ALSETLab/FluxPMU/00_Documentation/03_LabVIEW_VI_Documentation/24 Global Front Panel.pdf

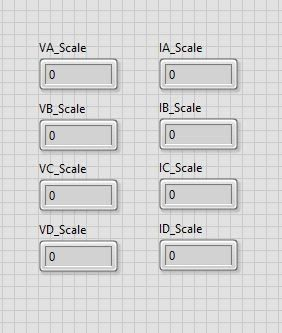
[picture p25: figure]

24 Global Front Panel is just used to output the global scale variables for voltages and currents a-d. The global variables are set in 43 Config File Get Input Scales. Note that 24 Global Front Panel does not have a block diagram, as the only output is from global variables.
