ALSETLab/FluxPMU/00_Documentation/03_LabVIEW_VI_Documentation/33 GPS Time to Labview Time.pdf

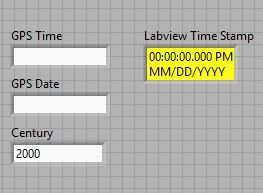
[picture p26: figure]

33 GPS Time to LabVIEW Time takes three inputs, the GPS Time, GPS Date, and the Century to output the time in a similar format in LabVIEW, used for creating a global time variable to create the synchrophasors. The Front Panel (above) displays all of this information.

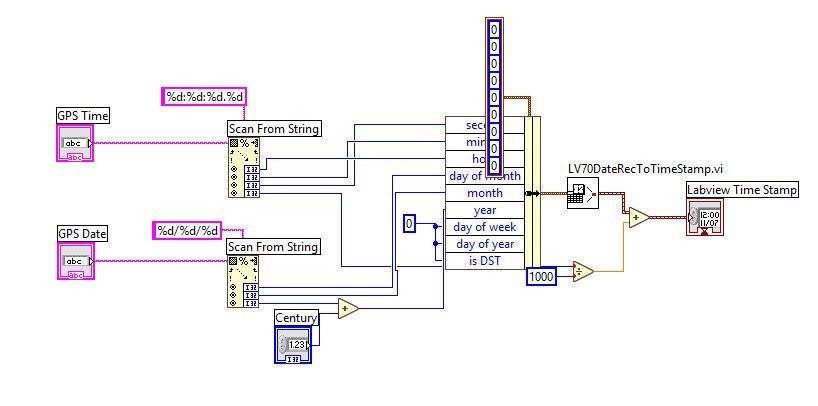
[picture p27: figure]

The Block Diagram (above) starts with the input GPS Time and GPS Date. ATTENTION: The GPS Time must be input in the format HR:MIN:SS.MSS The Date must be input in the format DD/MM/YY NOT MM/DD/YYYY. Both the GPS Time and GPS Date are converted into strings based on the format as stated in ATTENTION. Each string value excluding the millisecond time is bundled to a cluster, and converted into a LabVIEW Time Stamp. LabVIEW Time Stamp does not support millisecond when bundling, so the millisecond value is added to the Time Stamp once it has been created. The Time Stamp is then sent to the Front Panel as output. The output time has the same format as above, but the output date is sent in the format of MM/DD/YYYY
