ALSETLab/FluxPMU/00_Documentation/03_LabVIEW_VI_Documentation/34 GPS Time from Config.pdf

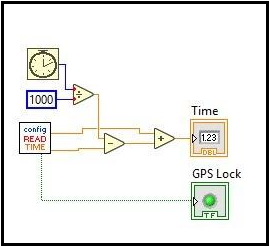
[picture p28: figure]

34 GPS Time from Config VI outputs the Time by first finding the difference between the Tick Count and the millisecond counter in microseconds. These values come from the VI 42 Config File Read GPS Time. The difference is added to the LabVIEW time to output the Time. The VI also outputs if the GPS lock is True or False based on 42 Config File Read GPS Time.
