ALSETLab/FluxPMU/00_Documentation/03_LabVIEW_VI_Documentation/15 Triple Phase Signal Generation.pdf

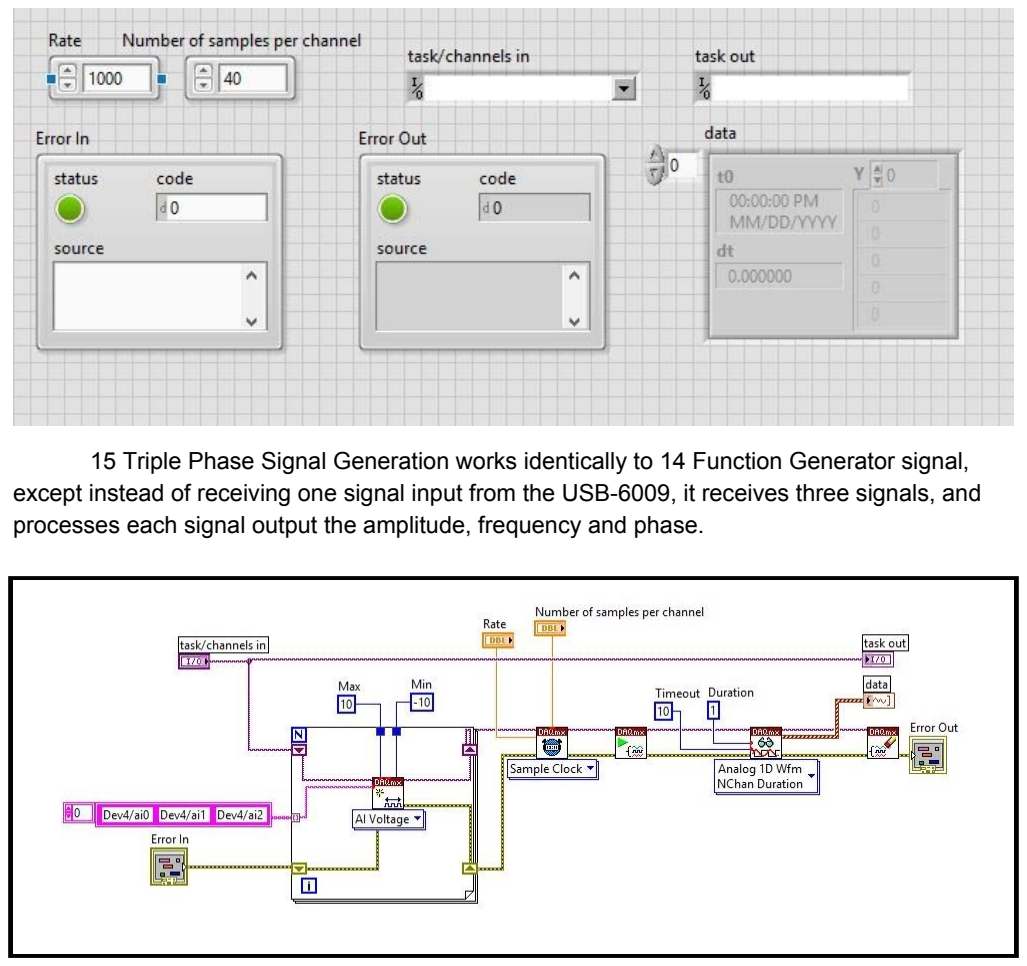
[picture p35: page 1]

15 Triple Phase Signal Generation works identically to 14 Function Generator signal, except instead of receiving one signal input from the USB-6009, it receives three signals, and processes each signal output the amplitude, frequency and phase.
