ALSETLab/FluxPMU/00_Documentation/03_LabVIEW_VI_Documentation/30 GPS Time Fetch.pdf

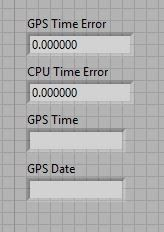
[picture p38: figure]

30 GPS Time Fetch is used to find the time in order to create a time synchronous system. The image above shows the Front Panel. The GPS Time, Date, and Time Error are outputted, along with the CPU Time Error.

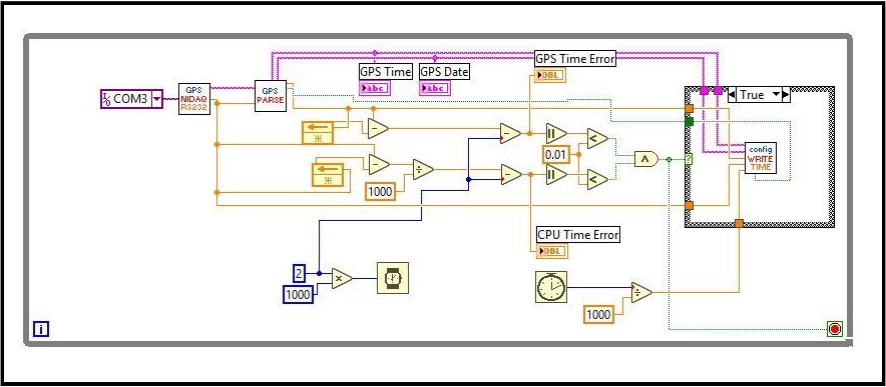
[picture p39: figure]

ATTENTION: The I/O COM# may have to be changed for your Garmin GPS set up.

Above shows the Block Diagram. 30 GPS Time Fetch continuously finds the time from the Garmin GPS signal by using a While Loop, and several sub-VIs to determine a synchronous time. GPS Time Fetch begins by receiving an input the Garmin GPS at a COM input port. You will need to set the port number here, based on what port you plug the RS-232 Cable into. Use Windows Device Manager to easily find what port number you need.
Two signals are sent:
- The Pink Line, the GPS data is sent to 31GPS NIDAQ RS232 sub-VI for Data processing. The output data of the sub-VI is sent to another sub-VI, 32 GPS PARSE, for further processing. 32 GPS PARSE outputs the Time, Date, which are sent to the Front Panel, and to the Case Structure.
- The Orange Line, the CPU data, is sent through various logic structures to calculate both the GPS Time Error and the CPU Time Error, which are sent to the Front Panel. If both the errors satisfy the condition of being less than 0.01 two things happen. The Case Structure is satisfied, and writes all of the data found to 41 Config File Write GPS Time, and the while loop stops.
Once computed, the GPS Time Error, CPU Time Error, GPS Time and GPS Date are all written via 41 Config File Write GPS Time, to be used by 34 GPS Time From Config in processing the time.
