ALSETLab/FluxPMU/00_Documentation/03_LabVIEW_VI_Documentation/31 GPS Interrupt RS232 Read.pdf

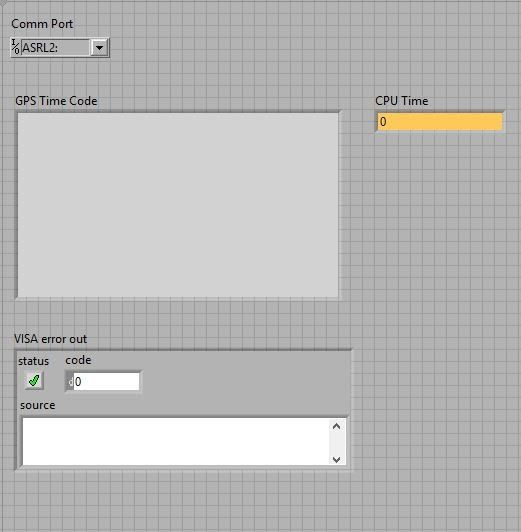
[picture p40: figure]

31 GPS Interrupt RS232 Read takes a COM port and uses the VISA program to produce the GPS Time Code. The Time code is sent to various other VIs to be used as the time Synchronous component in analysis.

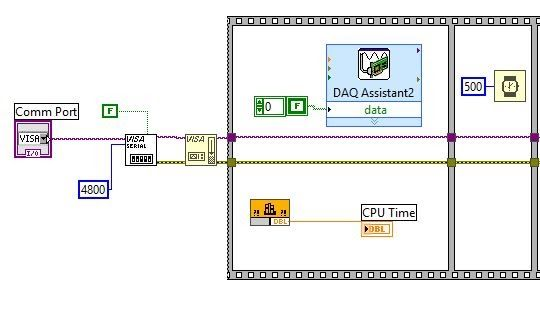
[picture p41: figure]

The VI starts by receiving the port resource name, or the COMM port specified in 30 GPS Time Fetch. The port information is sent to the VISA Configure Serial Port, which also is inputted with the baud rate. The VISA resource name and any errors are sent through a VISA buffer. After the buffer, the Flat sequence portion of code is activated. The first box uses the NI_Timer.dll to find the CPU time, which is used to compare to the GPS time. The DAQ Assistant 2 sets a task. The second box in the flat sequence waits for half a second.

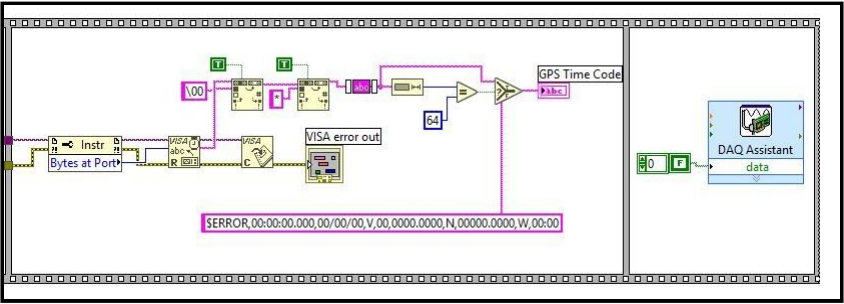
[picture p42: figure]

The third box in the flat sequence begins by receiving the VISA resource name, and returns the byte at that port. Both of these are sent to a buffer, which returns the resource name again, and the data at the port in a read buffer as a string. In the bottom portion, the VISA is closed, and any errors are sent to the Front Panel. In the above portion, the string is sent to a search and replace in the string twice. Once complete, the whitespace is trimmed, and the length is calculated. Based on the length, either the correct GPS Time code is produced, or an Error code is returned. Once complete, the final part of the flat sequence closes the task.

When you run the VI you have to make sure to NOT have HyperTerminal/Access running at the same time. If a Hyper program is running, you will get a VISA error, stating that the GPS signal cannot be accessed. Even if everything else is set up/running correctly, if either of the Hyper programs are connected, this VI will not work.
When you run the VI with either Hyper program connected, the GPS time code will be outputted in the Hyper Program, as shown below.

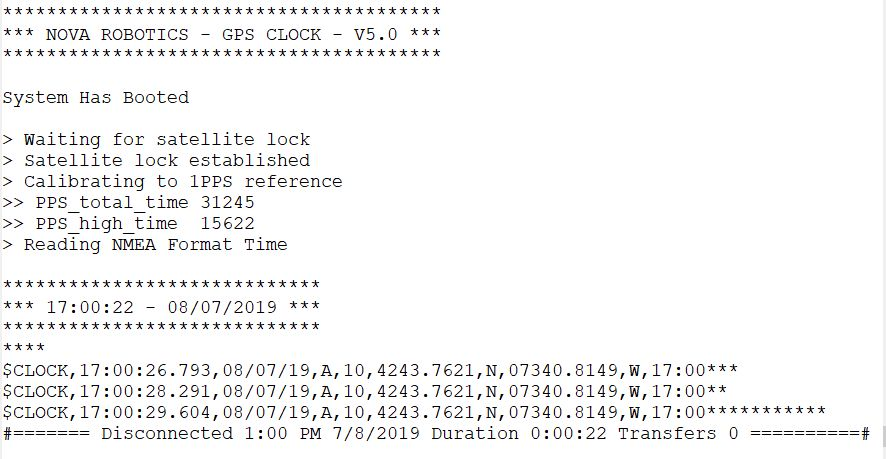
[picture p43: figure]

The image above shows the output when connecting simultaneously being connected to HyperAccess and LabVIEW. Each GPS time code line represents running the VI once.
