ALSETLab/FluxPMU/00_Documentation/03_LabVIEW_VI_Documentation/38 Date Conversion.pdf

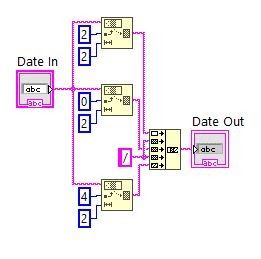
[picture p52: figure]
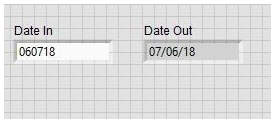
[picture p53: figure]

38 Date Conversion works in a similar manner to 37 Time Conversion. The Date string is inputted and split, as the input date is represented by DDMMYY. The split strings are concatenated, along with adding ‘/’ in between each two characters, to output the correct Date data in the format MM/DD/YY.
