ALSETLab/FluxPMU/00_Documentation/03_LabVIEW_VI_Documentation/40 Config File Path.pdf

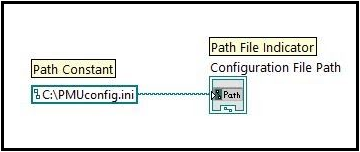
[picture p57: figure]

ATTENTION: The Path Constant will have to change based on YOUR file locations.

40 Config File Path is used to set the right path for OpenPMU files to communicate. The image on the left shows the Path Constant on the Front Panel. The image on the right shows the Path Constant set in the Block Diagram. ATTENTION: The Path Constant will have to change based on YOUR file locations. The Path Constant is given to the file path indicator, which sets the file path for the OpenPMU programs to use.
