ALSETLab/FluxPMU/00_Documentation/03_LabVIEW_VI_Documentation/42 Config File Read GPS Time.pdf

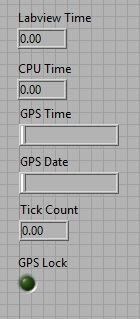
[picture p60: figure]

42 Config File Read GPS Time VI outputs various variables written to GPS_time.ini in the VI 41 Config File Write GPS Time and outputs those values to the Front Panel.

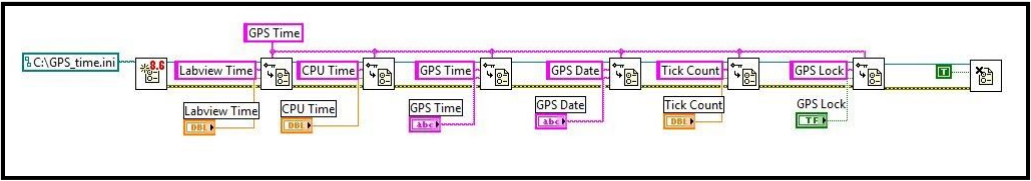
[picture p61: figure]

The VI starts with a configuration file path that is mapped to a reference number using the sub VI Open Config Data(compatibility). Each value associated with a key (Labview Time, CPU Time etc.) is read and sent as output to the Front Panel. If no key is not found, a 0 is returned. Any errors associated with the process are sent through each key as error in and error out. Once complete, the configuration file is closed, and no new file is written, indicated by the False constant.
