ALSETLab/FluxPMU/00_Documentation/03_LabVIEW_VI_Documentation/_02 Triple Waveform Simulation.pdf

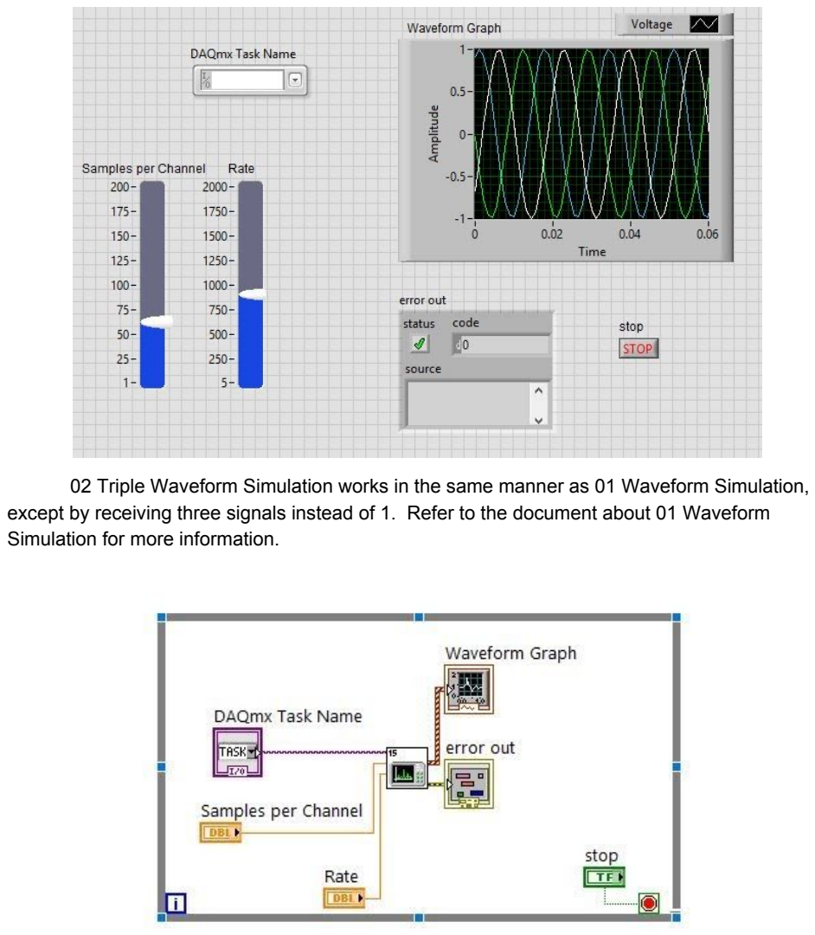
[picture p66: page 1]

02 Triple Waveform Simulation works in the same manner as 01 Waveform Simulation, except by receiving three signals instead of 1. Refer to the document about 01 Waveform Simulation for more information.
