ALSETLab/FluxPMU/00_Documentation/03_LabVIEW_VI_Documentation/Code Flow Chart.pdf

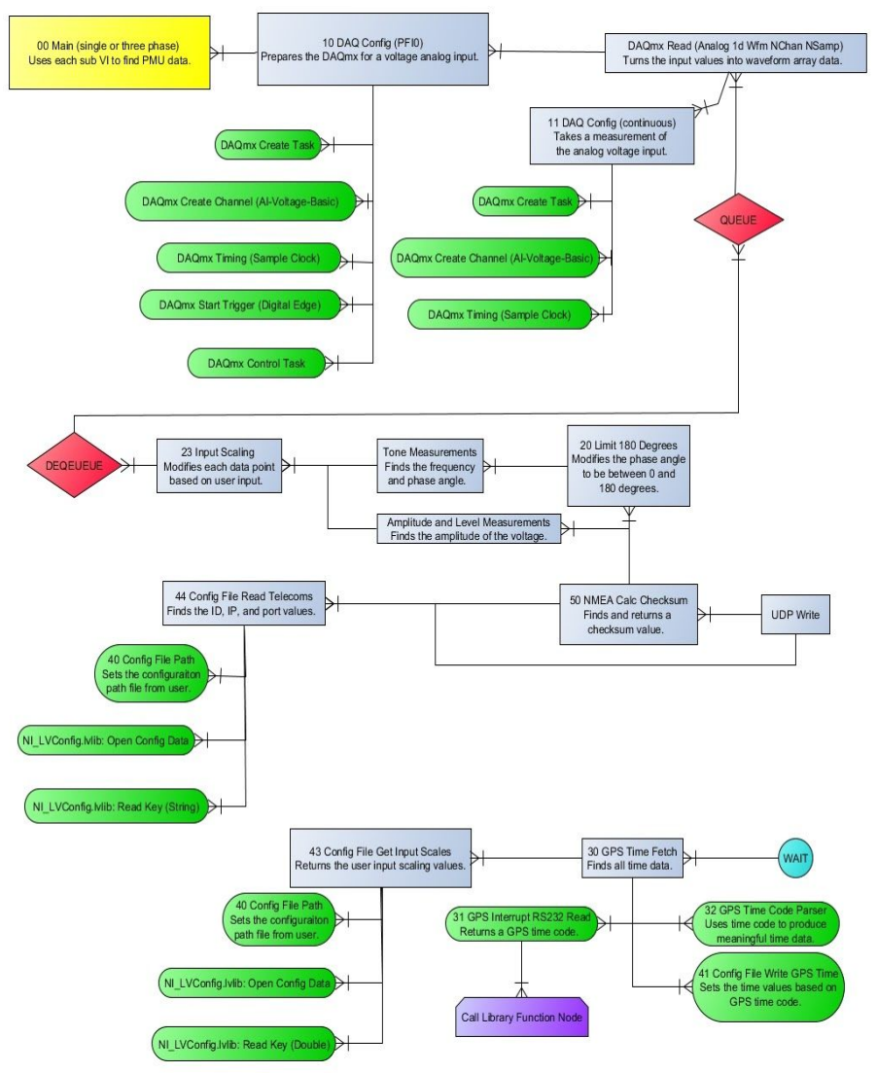
[picture p67: figure]
