ALSETLab/FluxPMU/00_Documentation/03_LabVIEW_VI_Documentation/21 Symmetrical Components .pdf

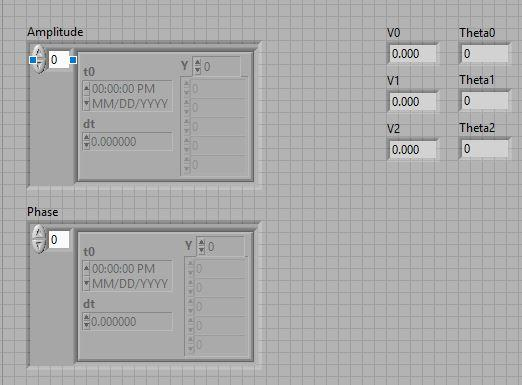
[picture p70: figure]

21 Symmetrical Components VI takes raw input from an NI-DAQmx as waveform data. The waveform data is manipulated to find the amplitudes and phases of each wave given to it.

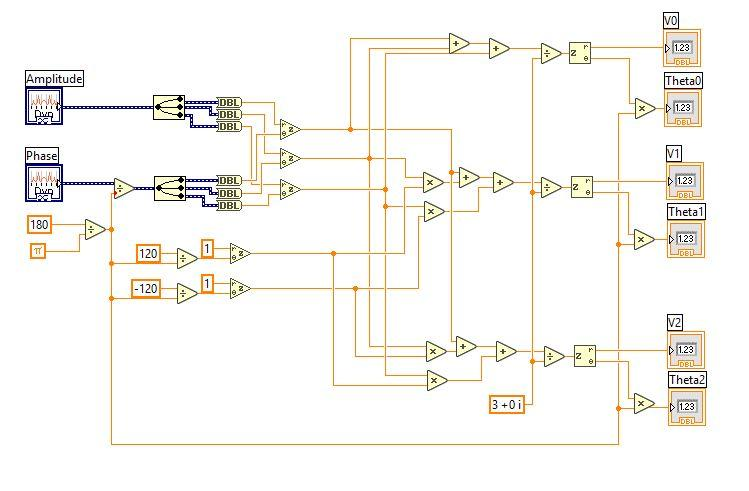
[picture p71: figure]

The VI starts by receiving raw Amplitude and Phase data from an NI-DAQmx. Each signal is split into 3 data waves. Each phase angle and amplitude value for each signal 1, 2, and 3 are converted into complex notation of r*e^(i*theta), or phasor notation. The various outputs are then calculated by adding and modifying the complex notations. Once added and modified, the average is found, which is converted back to polar coordinates of amplitude and angle. These values are sent as outputs.
